Seborah/FF1/IMG_3568.jpg

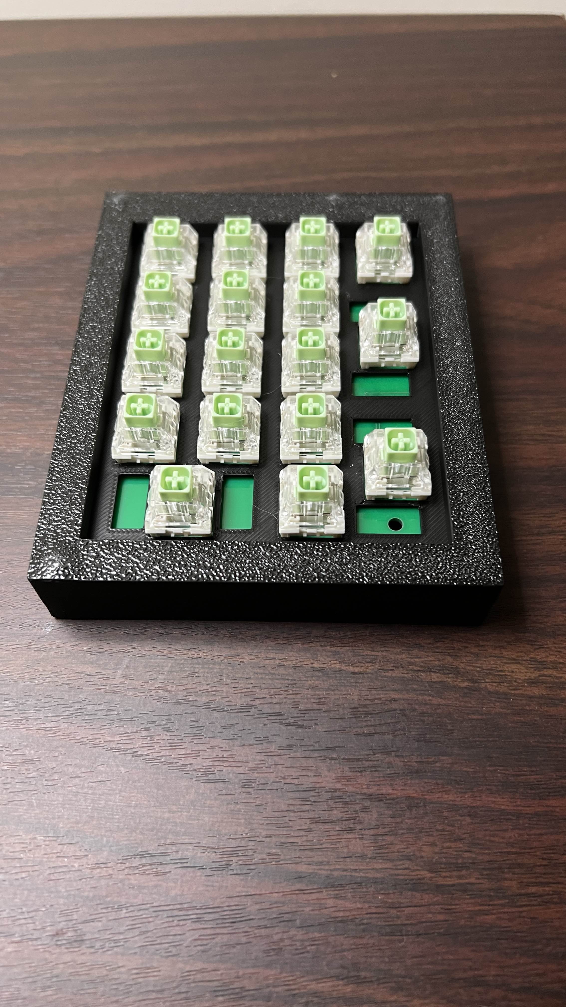
IMG_3568.jpg
