Seborah/FF1/IMG_3571.jpg

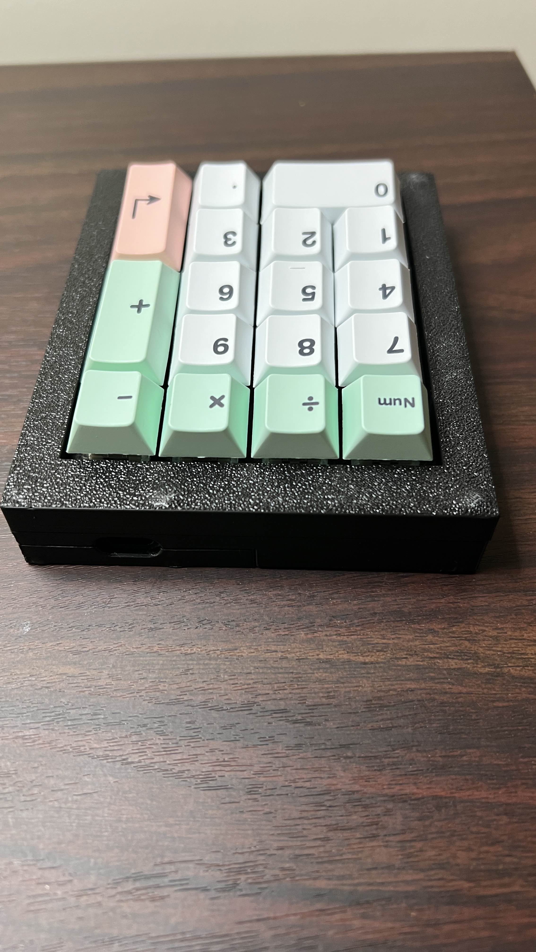
IMG_3571.jpg
